davw4453/Tube-Amplifier-Project/Simulations/6.3V-rectifier.asc

C1: cap; 100µ
C2: cap; 100n
D1: diode
D2: diode
D3: diode
D4: diode
R1: res; 1000000
R2: res; 18.8
R3: res; 18.8
R4: res; 7.875
V1: voltage; SINE(0 6.3 60)
Named nets: 0
.tran 200m
