davw4453/Tube-Amplifier-Project/Simulations/DC-Power.asc

C1: cap; 470µ
C2: cap; 470µ
D1: diode; 1N4007
D2: diode; 1N4007
D3: diode; 1N4007
D4: diode; 1N4007
R1: res; 1m
V1: voltage; SINE(0 340 60)
Named nets: 0
.tran .2
