davw4453/Tube-Amplifier-Project/Simulations/PowerAmp/CommonCathode-singleend.asc

L1: ind; 625µ; Rser=5000
L2: ind; 1µ; Rser=8
R1: res; 450
R2: res; 8
R3: res; 1Meg
U1: tetrode; 7591
V1: voltage; SINE(0 18.41 1K); AC 1
V2: voltage; 170
Named nets: 0, Vin, VPP
.include ../include/7591.inc
.tran 4m
K1 L1 L2 1
