davw4453/Tube-Amplifier-Project/Simulations/PreAmp/SRPPwithFeedback.asc

C1: cap; 1µ
C2: cap; 1µ
C3: cap; 1µ
C4: cap; 200p
R1: res; 330
R2: res; 100K
R3: res; 330
R4: res; 330
R5: res; 330
R6: res; 330
R7: res; 560K
R8: res; 330
R9: res; 5K
R11: res; 2.5K
R12: res; 1Meg
R13: res; 2.5K
R14: res; 1Meg
U1: triode; ECC88
U2: triode; ECC88
U3: triode; ECC88
U4: triode; ECC88
V1: voltage; SINE(0 1.4 1K); AC 1
V2: voltage; 170
Named nets: 0, Vin, VPP, VoutH, Vout
.include ../include/ECC88.inc
Volume Control
Gain Control
.ac dec 100 100 20K
