davw4453/Tube-Amplifier-Project/Simulations/ToneControl/filterCircuit.asc

C1: cap; 220n
C2: cap; 10n
R1: res; 2.2K
R2: res; {P1}
R3: res; {10K - P1}
R4: res; 2.2K
R5: res; 2.2K
R6: res; 1K
R7: res; {P3}
R8: res; {10K - P3}
R9: res; 1K
R10: res; 100K
V1: voltage; SINE(0 39.15 10K); AC 1
Named nets: Vin, 0, Vout
.param P1=10K*0.5
.param P3=10K*0.5
.ac dec 100 1 50K
